niksaw/SenseView-IoT/images/dashboard/Co2 SC.png

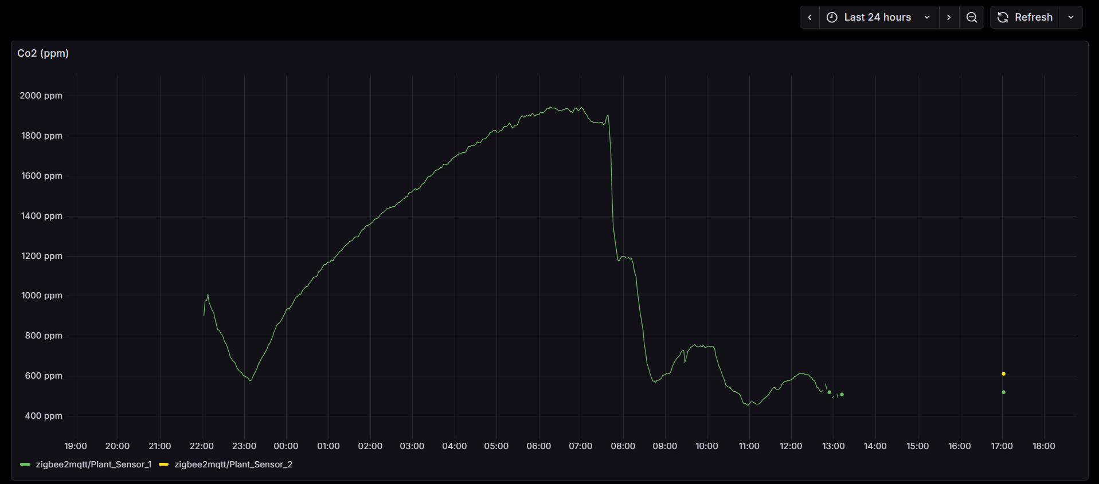
images/dashboard/Co2 SC.png
