niksaw/SenseView-IoT/images/dashboard/Humidity SC.png

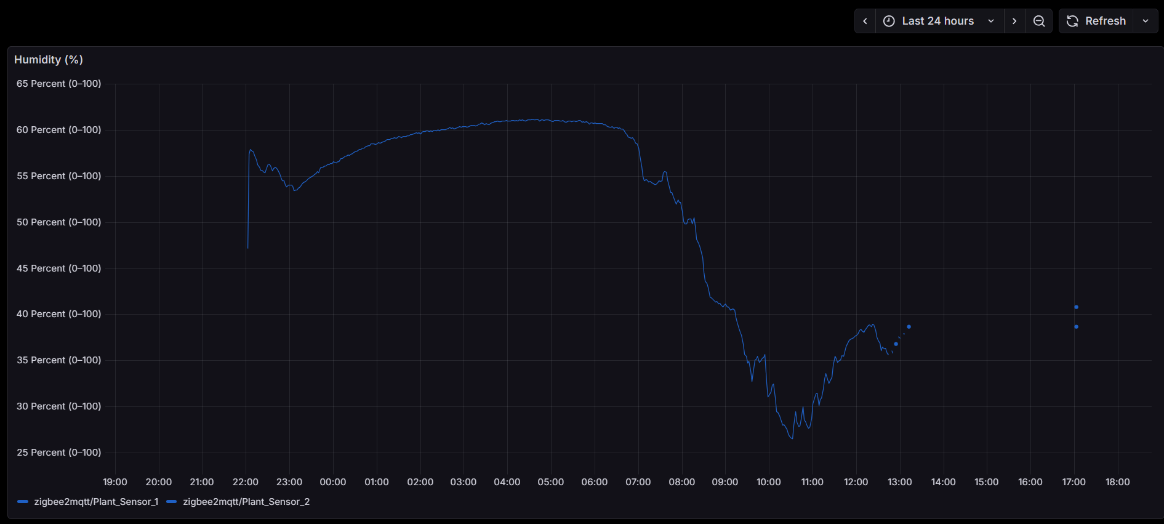
images/dashboard/Humidity SC.png
