niksaw/SenseView-IoT/images/dashboard/Pressure SC.png

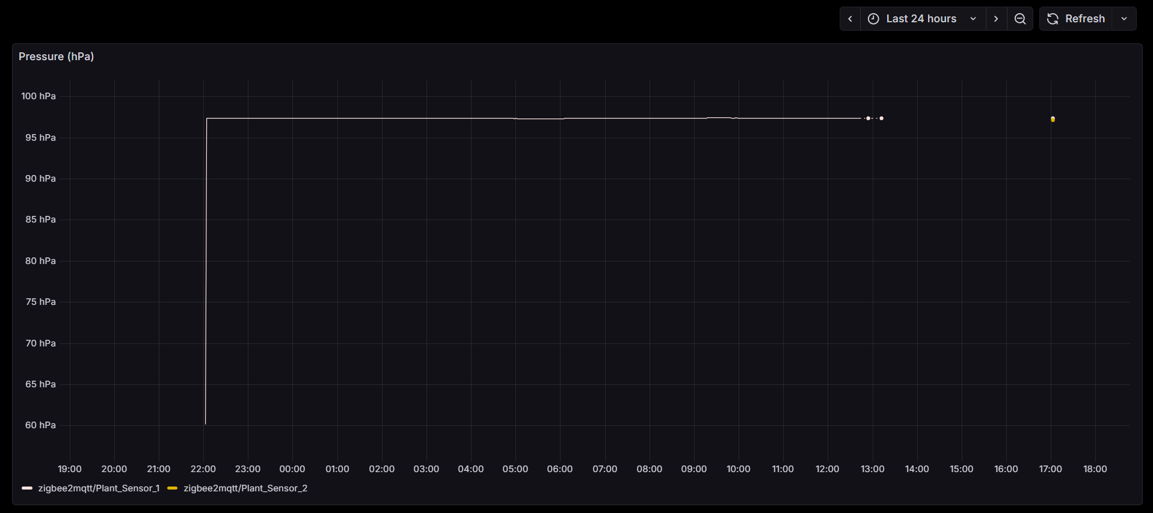
images/dashboard/Pressure SC.png
