niksaw/SenseView-IoT/images/dashboard/SC_MQTT Explorer.png

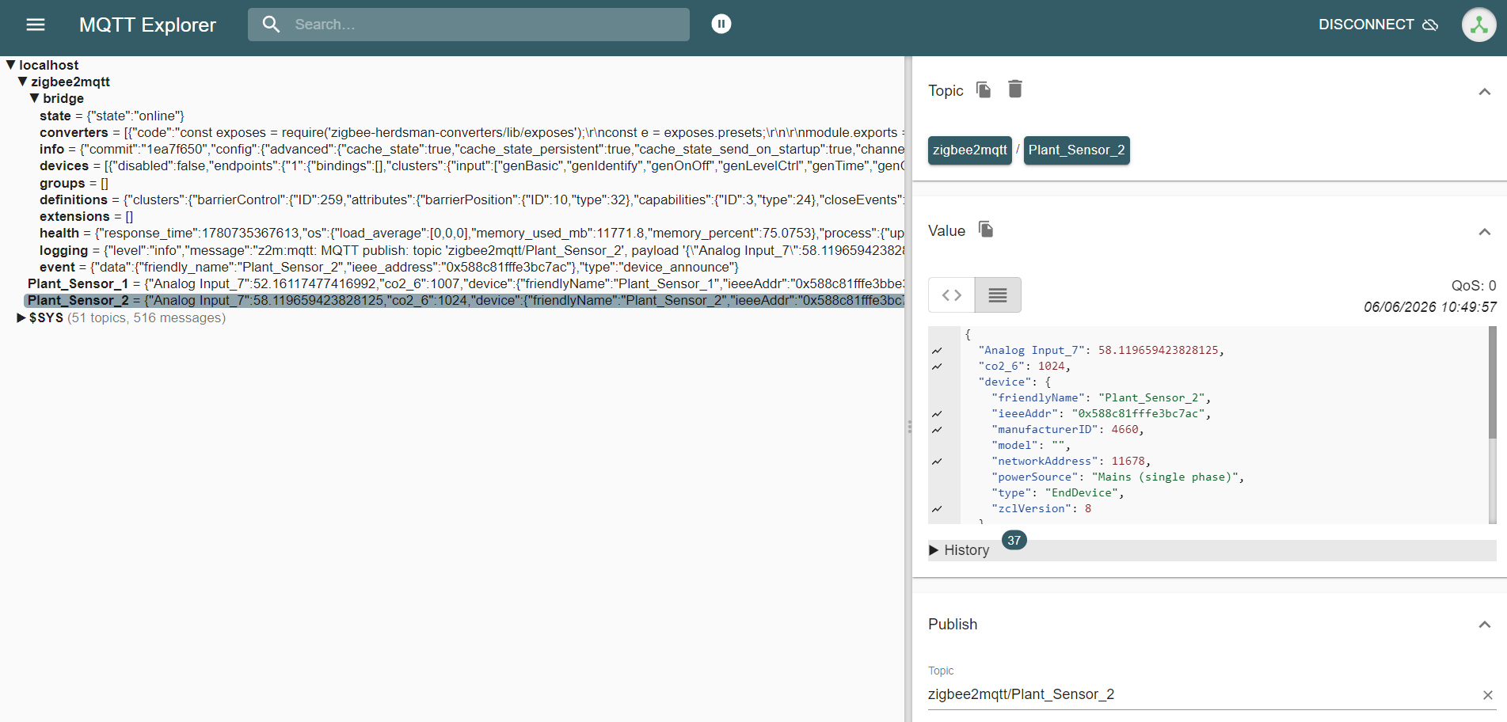
images/dashboard/SC_MQTT Explorer.png
