niksaw/SenseView-IoT/images/dashboard/Soil Moisture.png

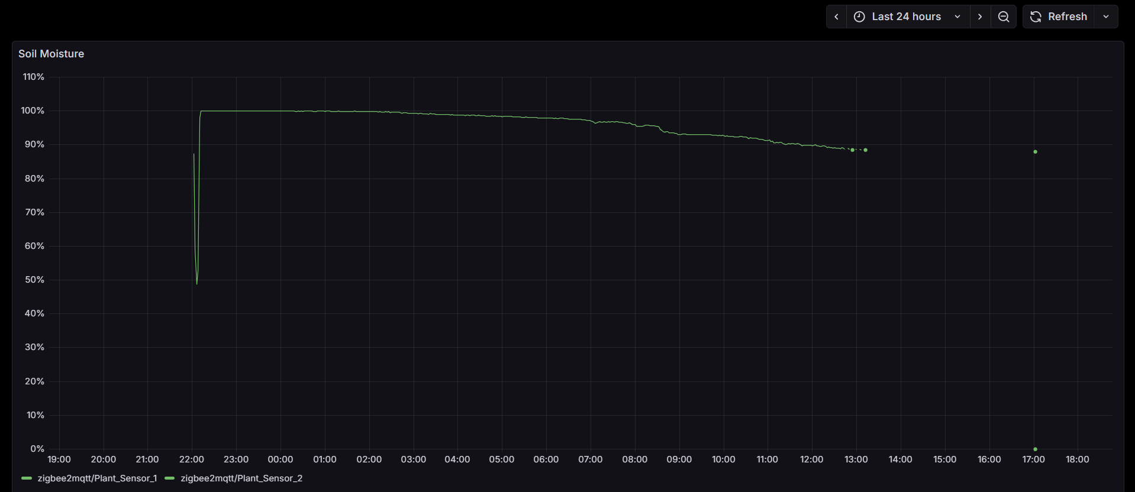
images/dashboard/Soil Moisture.png
