niksaw/SenseView-IoT/images/dashboard/Temperature SC.png

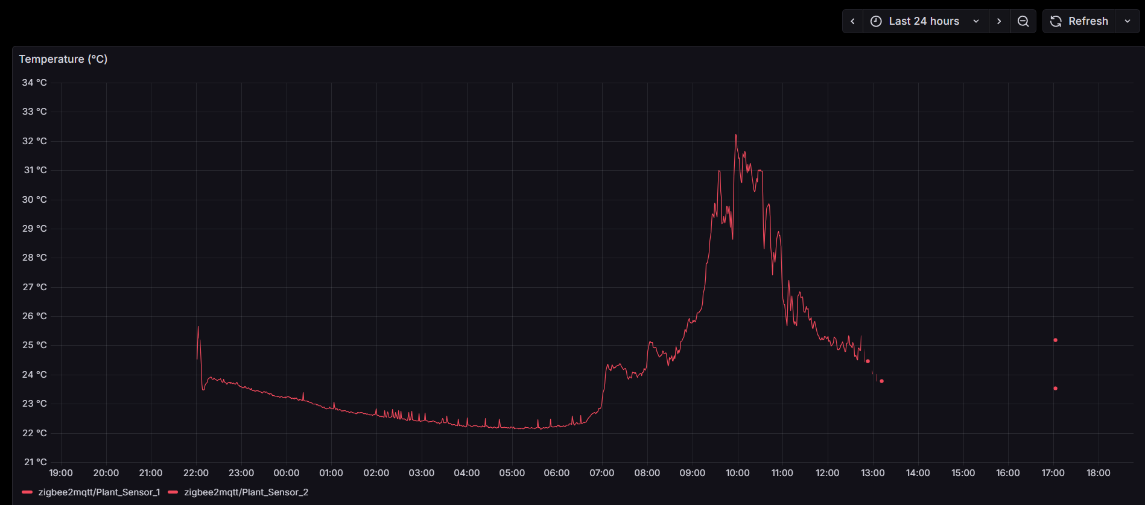
images/dashboard/Temperature SC.png
