niksaw/SenseView-IoT/images/hardware/pcb_assembly.jpeg.jpeg

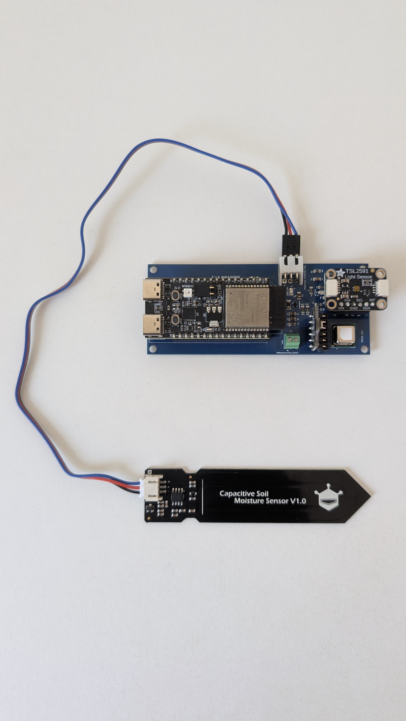
images/hardware/pcb_assembly.jpeg.jpeg
